incognitoforreview/TileScape/design_files/table design/table underside/webcam mount/0_readme_webcam_mount.pdf

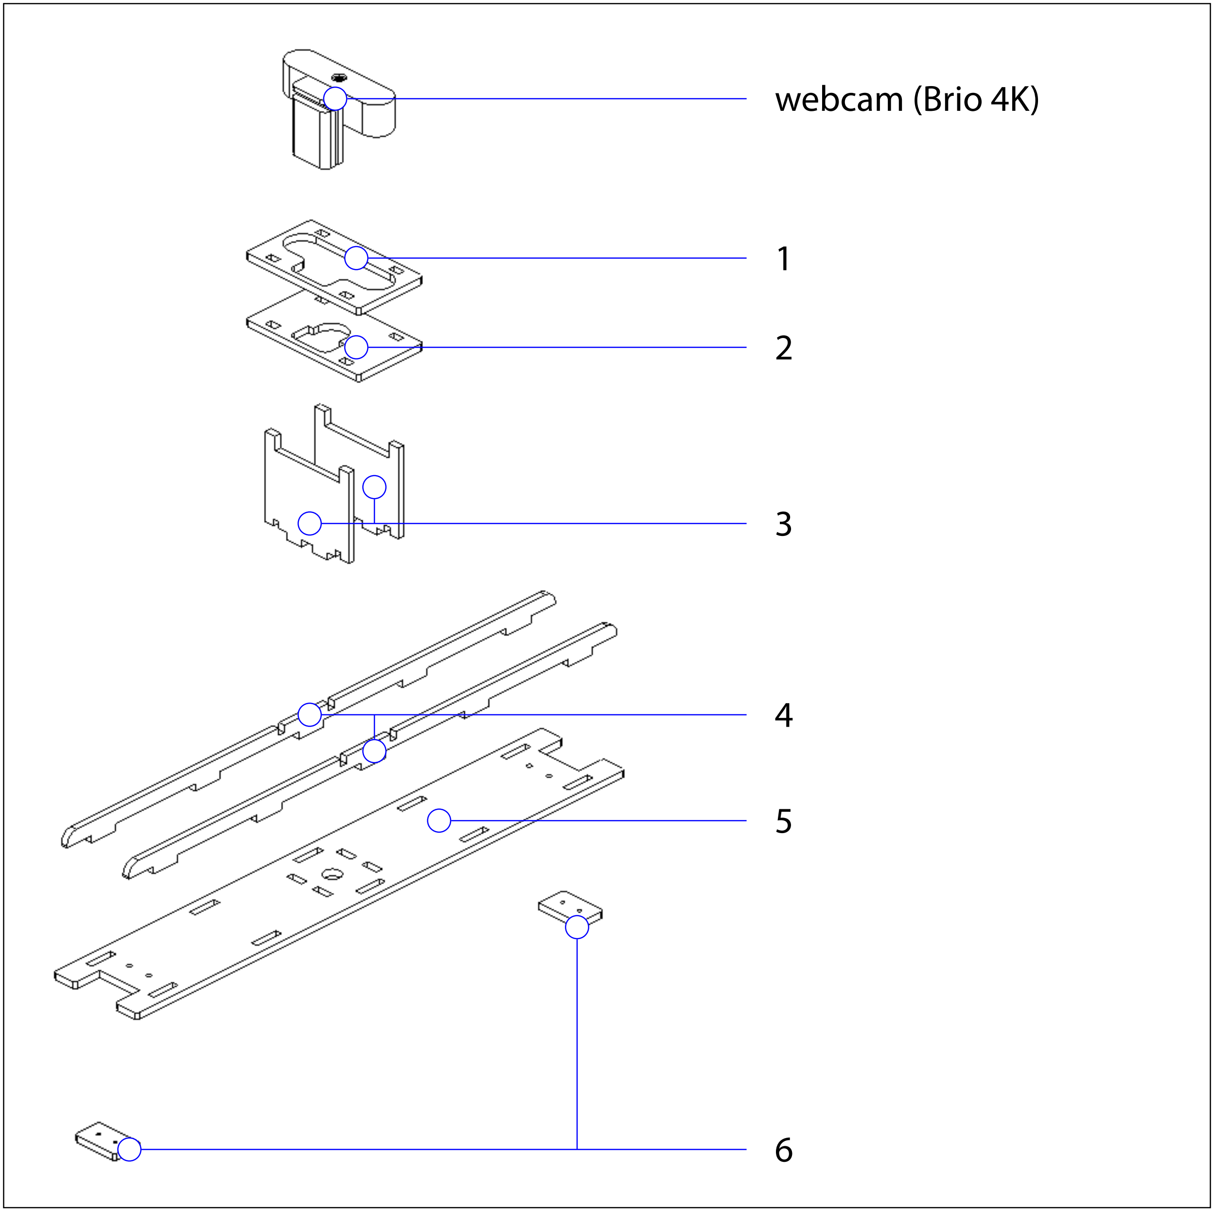
[picture p5: figure]
webcam (Brio 4K)

The les in this folder can be used to create the webcam mount for Tilescape’s tabletop. It is entirely constructed from laser cut shapes out of 6mm
wooden sheets. All shapes are included in a single le for laser cutting these shapes in dierent formats (.dxf, .pdf, .ai). In addition, one .pdf le has annotations in it that align with the numbers shown in the gure to the right.

Once all shapes are cut, the self-align and can be glued together. The exception to this is parts number 6, which are screwed to the middle of the 4_cross_beam_mount_x2 and are used for correct positioning when placing the assembled webcam mount (see gure of full tabletop system). No further nishing of the shapes is required.
