incognitoforreview/TileScape/design_files/table design/table surface/tabletop_frame_3.pdf

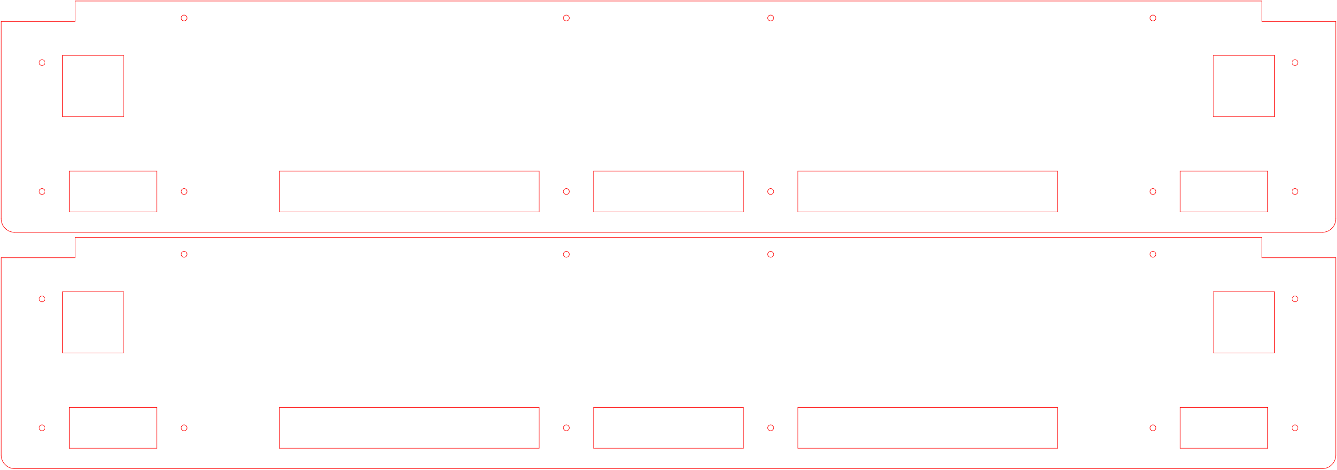
[picture p6: figure]
