incognitoforreview/TileScape/design_files/table design/table surface/tabletop_frame_3_annotated.pdf

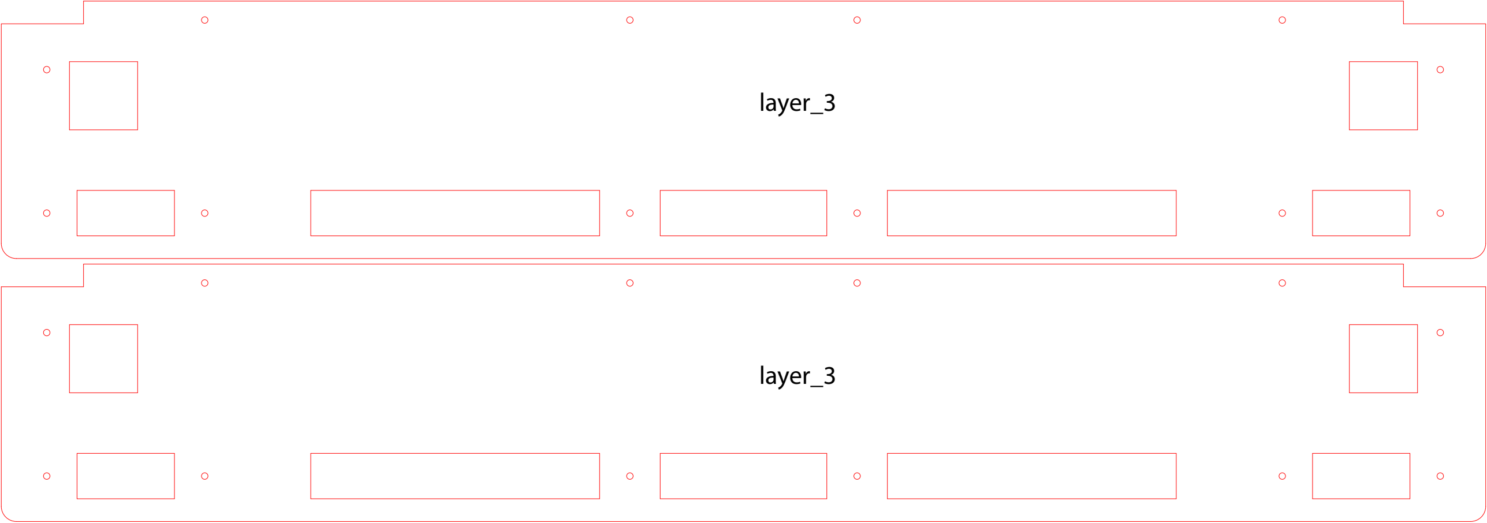
[picture p7: figure]
layer_3
