incognitoforreview/TileScape/design_files/table design/table underside/webcam mount/webcam_mount_laser_cut_shapes.pdf

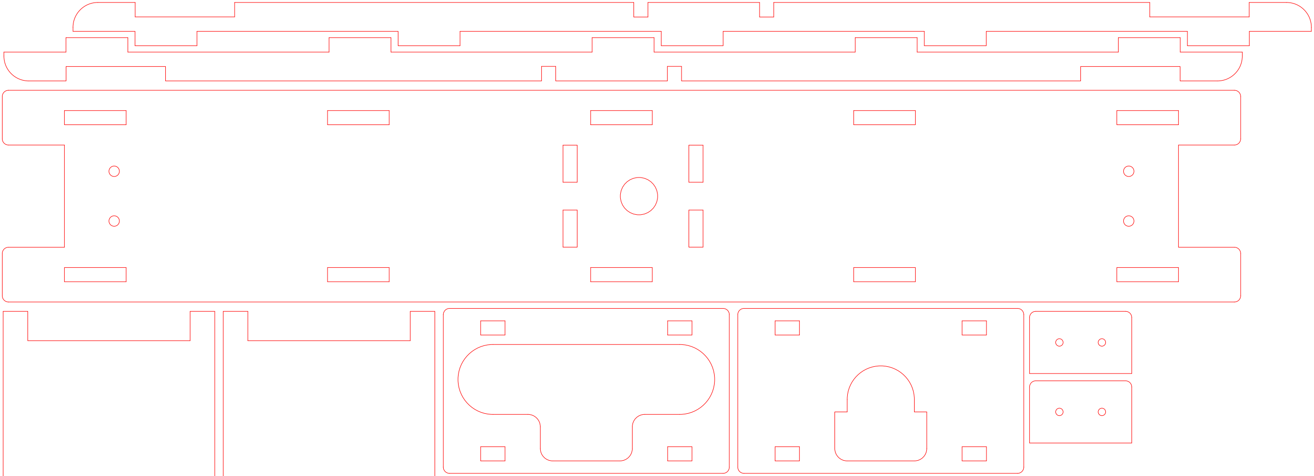
[picture p8: figure]
