incognitoforreview/TileScape/design_files/table design/table underside/webcam mount/webcam_mount_laser_cut_shapes_annotated.pdf

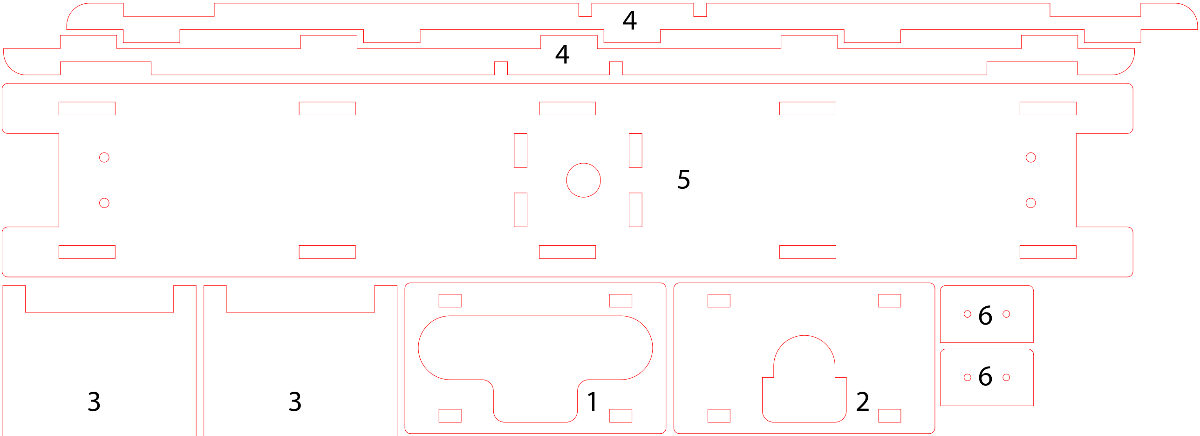
[picture p9: figure]
