incognitoforreview/TileScape/design_files/game pieces designs/3D print templates/2_additional_elevation_template.SLDPRT

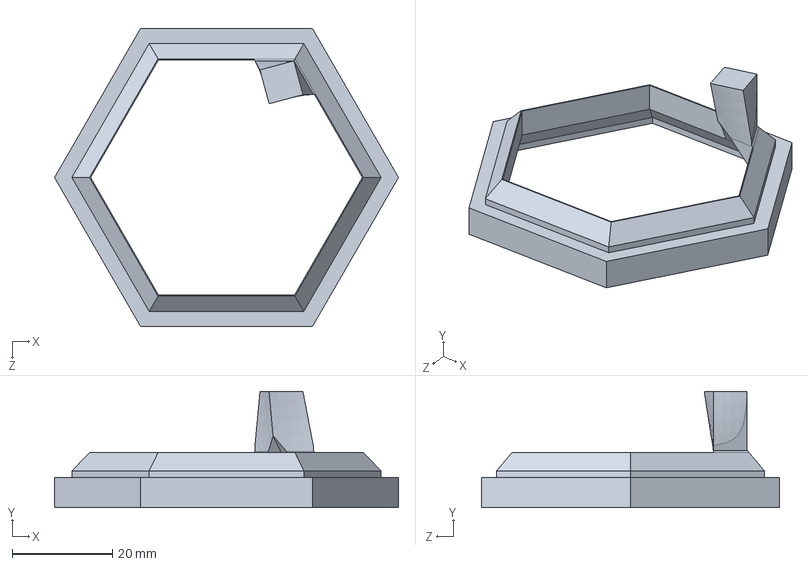
[picture p24: CAD file, 2026-01-09]
design_files/game pieces designs/3D print templates/2_additional_elevation_template.SLDPRT
68.7 x 23.2 x 59.5 mm
