incognitoforreview/TileScape/design_files/game pieces designs/laser cut templates/2_top_piece_base.dxf

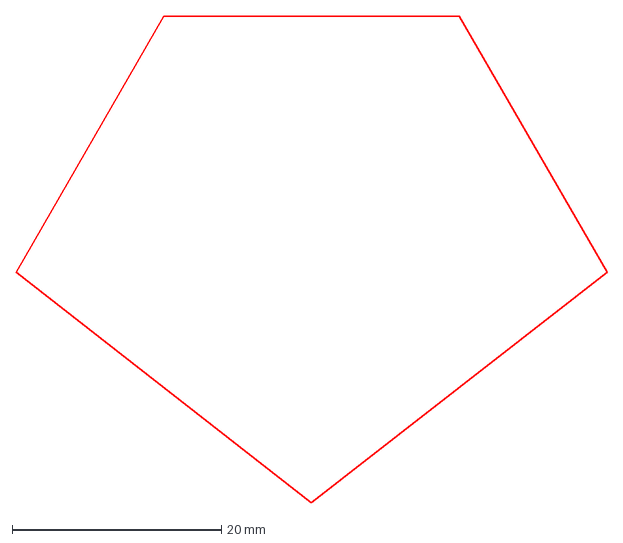
[picture p25: CAD file, 2026-01-09]
design_files/game pieces designs/laser cut templates/2_top_piece_base.dxf
56.5 x 46.5 mm
