incognitoforreview/TileScape/design_files/table design/projector and touchscreen frame/5_cross_beam_top.sldprt

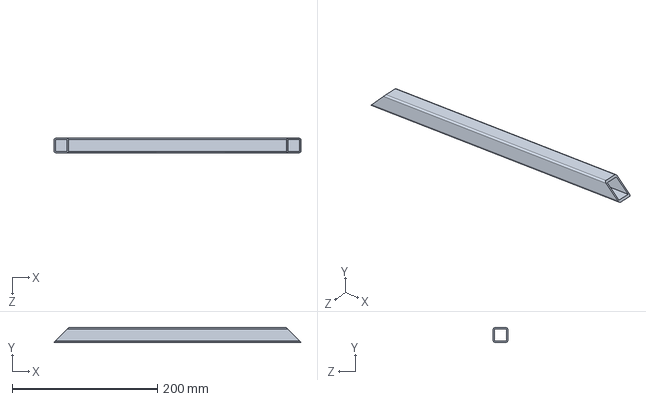
[picture p26: CAD file, 2026-01-09]
design_files/table design/projector and touchscreen frame/5_cross_beam_top.sldprt
340.2 x 20.0 x 20.0 mm
