incognitoforreview/TileScape/design_files/table design/table surface/tabletop_frame_3.dxf

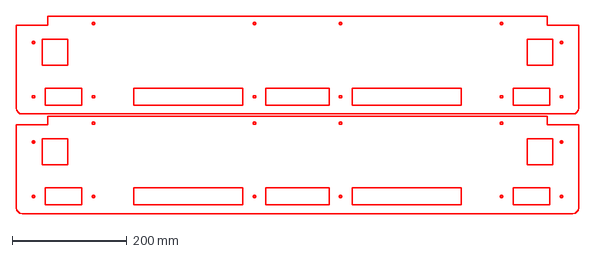
[picture p27: CAD file, 2026-01-09]
design_files/table design/table surface/tabletop_frame_3.dxf
980.0 x 343.6 mm
