incognitoforreview/TileScape/design_files/game pieces designs/laser cut templates/1_height_piece.dxf

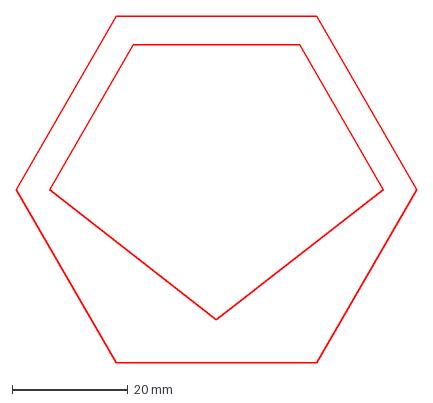
[picture p28: CAD file, 2026-01-09]
design_files/game pieces designs/laser cut templates/1_height_piece.dxf
69.3 x 60.0 mm
