incognitoforreview/TileScape/design_files/table design/table surface/hexagon_grid_6mm.dxf

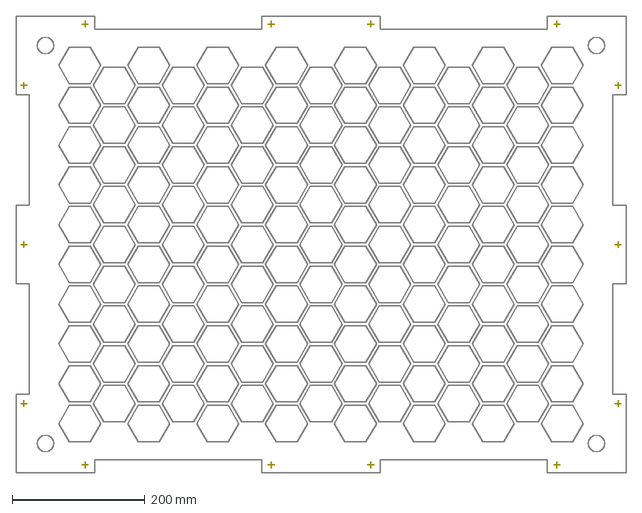
[picture p29: CAD file, 2026-01-09]
design_files/table design/table surface/hexagon_grid_6mm.dxf
920.0 x 689.0 mm
