incognitoforreview/TileScape/design_files/game pieces designs/laser cut templates/3_no_elevation_base.dxf

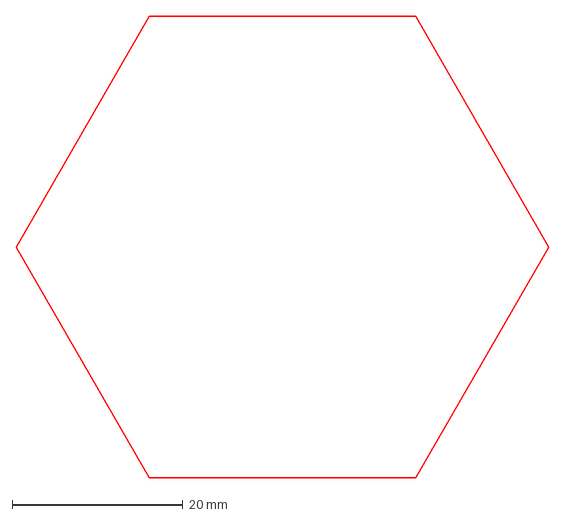
[picture p30: CAD file, 2026-01-09]
design_files/game pieces designs/laser cut templates/3_no_elevation_base.dxf
62.4 x 54.0 mm
