incognitoforreview/TileScape/design_files/table design/table surface/tabletop_frame_5.dxf

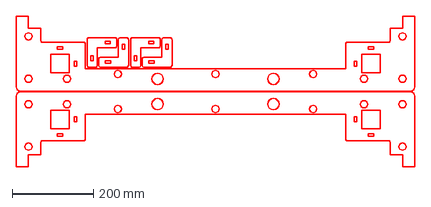
[picture p31: CAD file, 2026-01-09]
design_files/table design/table surface/tabletop_frame_5.dxf
980.0 x 371.0 mm
