incognitoforreview/TileScape/design_files/table design/table underside/legs & frame/0_readme_tabletop_underside_assembly.pdf

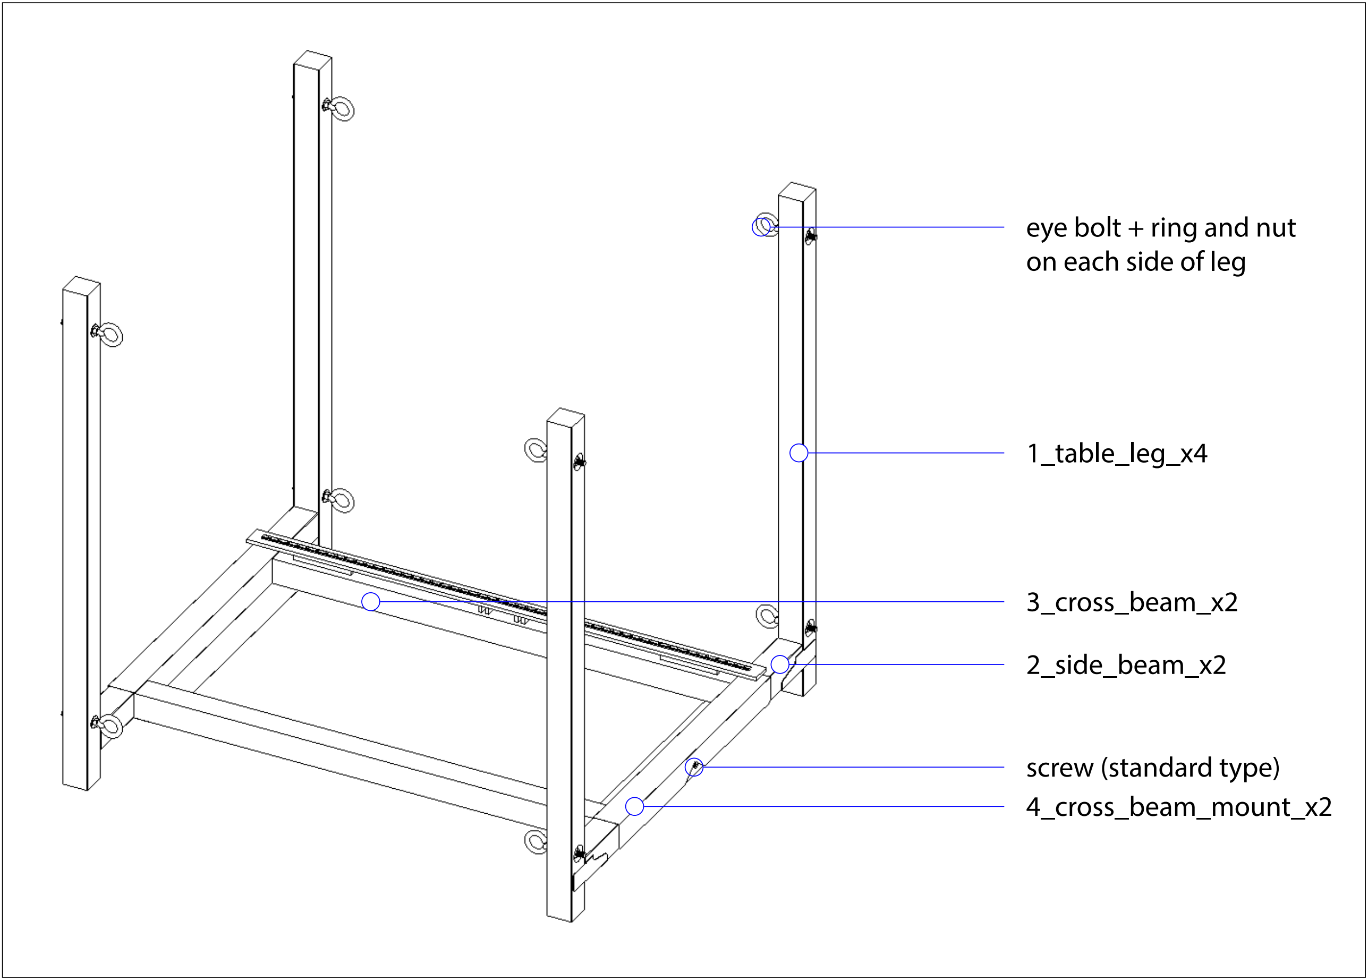
[picture p35: figure]
1_table_leg_x4; eye bolt + ring and nut on each side of leg; 2_side_beam_x2; 4_cross_beam_mount_x2; screw (standard type); 3_cross_beam_x2

The les in this folder can be used to create the legs and frame for mounting Tilescape’s tabletop.
It is mainly constructed from wooden beams and standard connection materials like screws. Only the 4_cross_beam_mount_x2 is manufactured from a 1mm steel plate by means of cutting, bending and drilling.

For construction, the gure on the right shows the assembly underneath the tabletop. In the folder,
the drawings for the beams and dimensions can be found. Two 1_table_leg_x4 and one 2_side_beam_x2 are connected twice to create two U form shapes. We used a metal connection bought at a hardware store (visible in the gure), but simple screws suce. The two 3_cross_beam_x2 are connected with screws to the 4_cross_beam_mount_x2 to create a rectangular shape. Drill holes for this on the bottom side of 4_cross_beam_mount_x2. The two U shapes and rectangular shape can now be placed on each other. We added a simple screw in the middle of
each 2_side_beam_x2 (highlighted in the gure) to help positioning. We recommend painting all wooden beams black with a matte nish before assembly.

The eye bolt, rings and nuts (highlighted in the gure) are used to add 8 connection points for steel cross wires and for the curtain to wrap the table. We used 8mm diameter standard materials from a hardware store.
