incognitoforreview/TileScape/design_files/table design/table surface/tabletop_frame_2.pdf

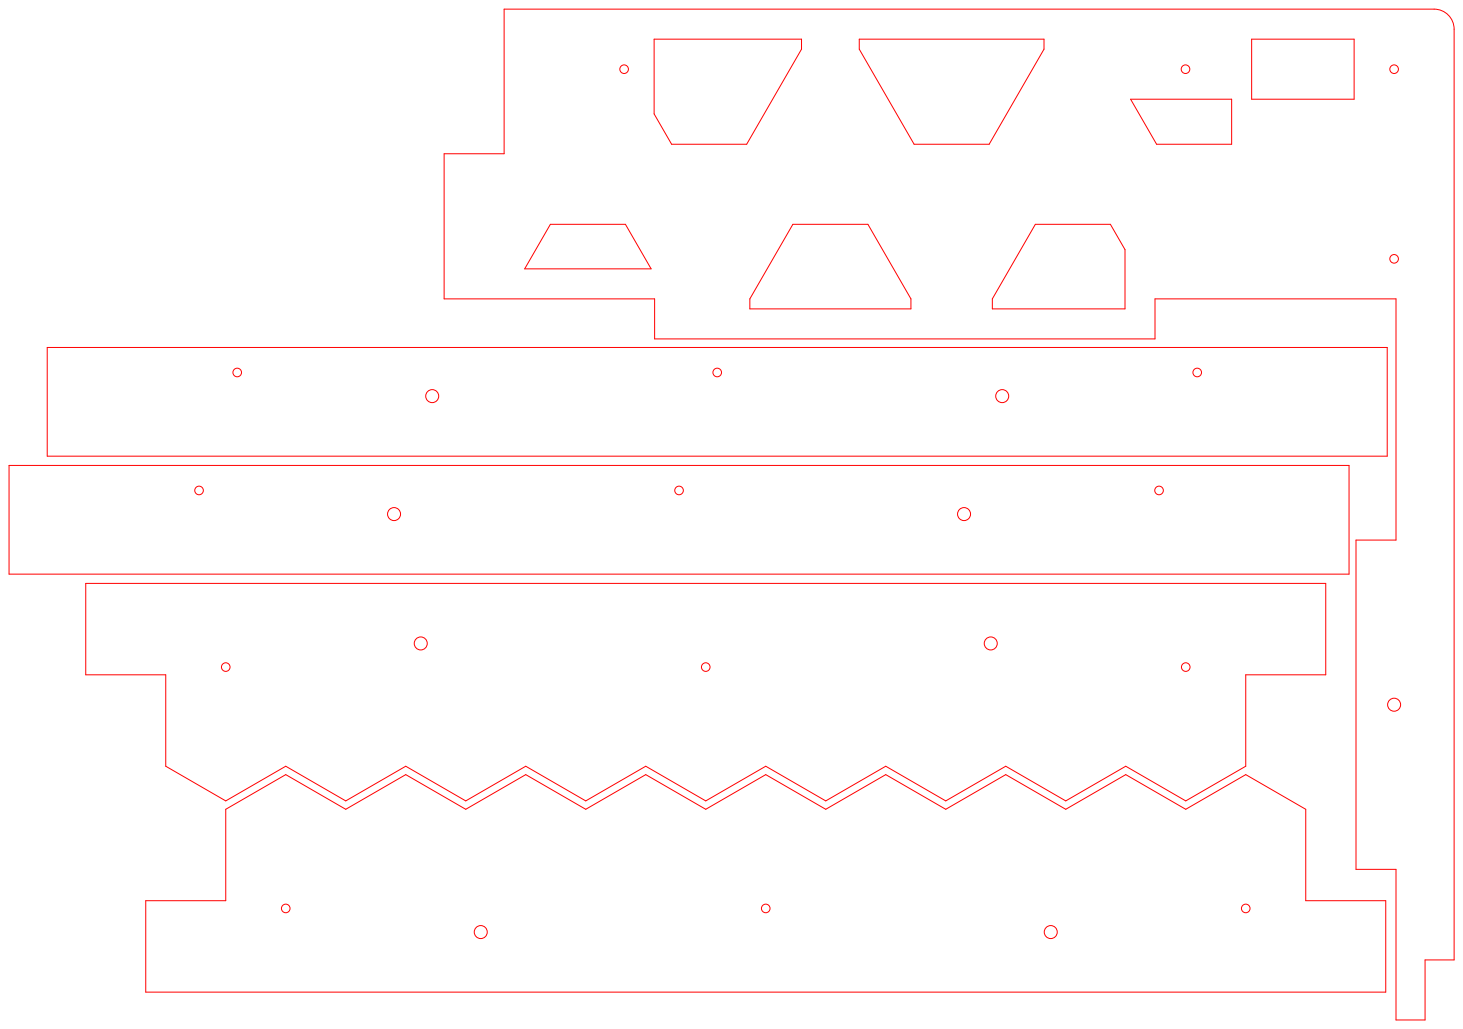
[picture p39: page 1]
