incognitoforreview/TileScape/design_files/table design/table surface/tabletop_frame_2_annotated.pdf

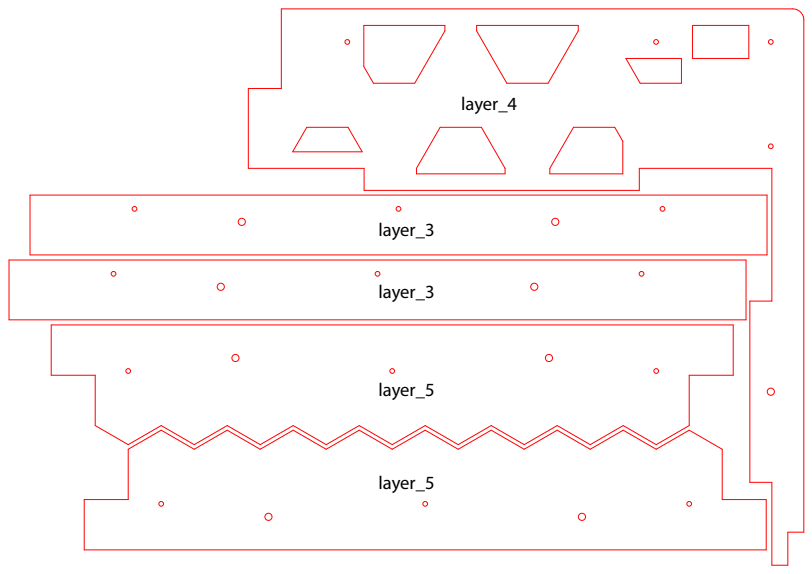
[picture p40: page 1]
layer_4; layer_3; layer_5
