incognitoforreview/TileScape/design_files/table design/table surface/tabletop_frame_4.pdf

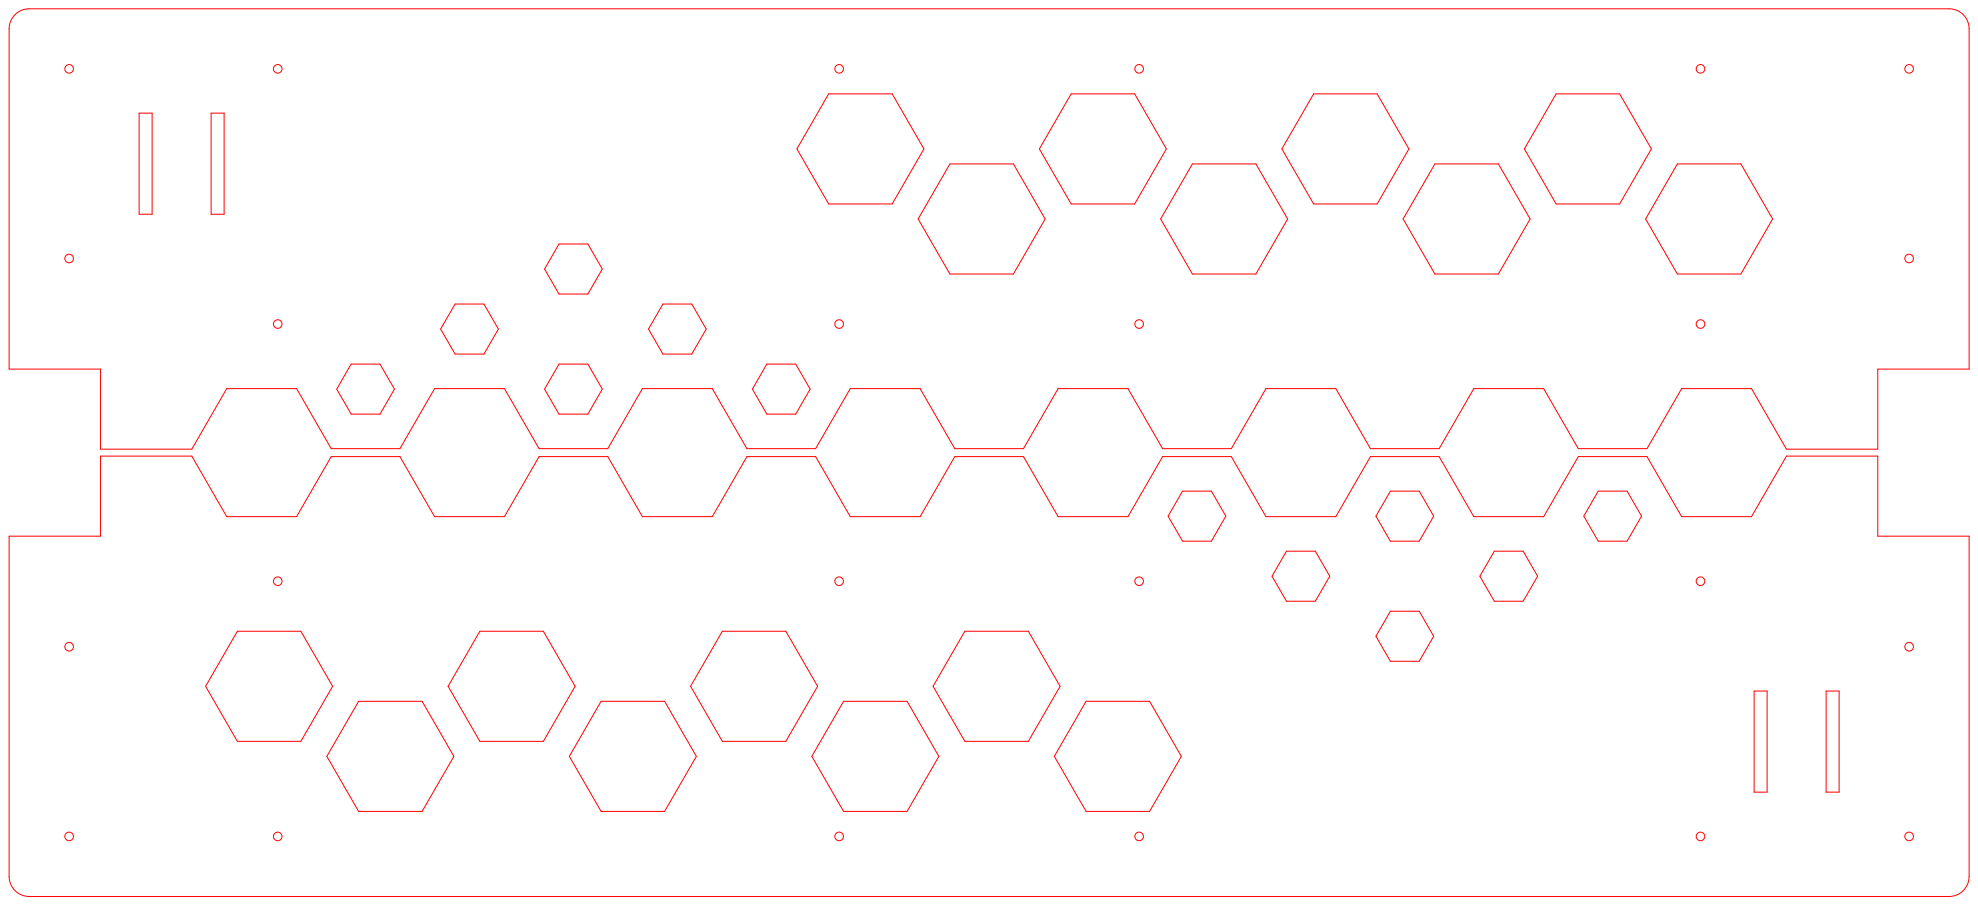
[picture p41: page 1]
