incognitoforreview/TileScape/design_files/table design/table surface/tabletop_frame_4_annotated.pdf

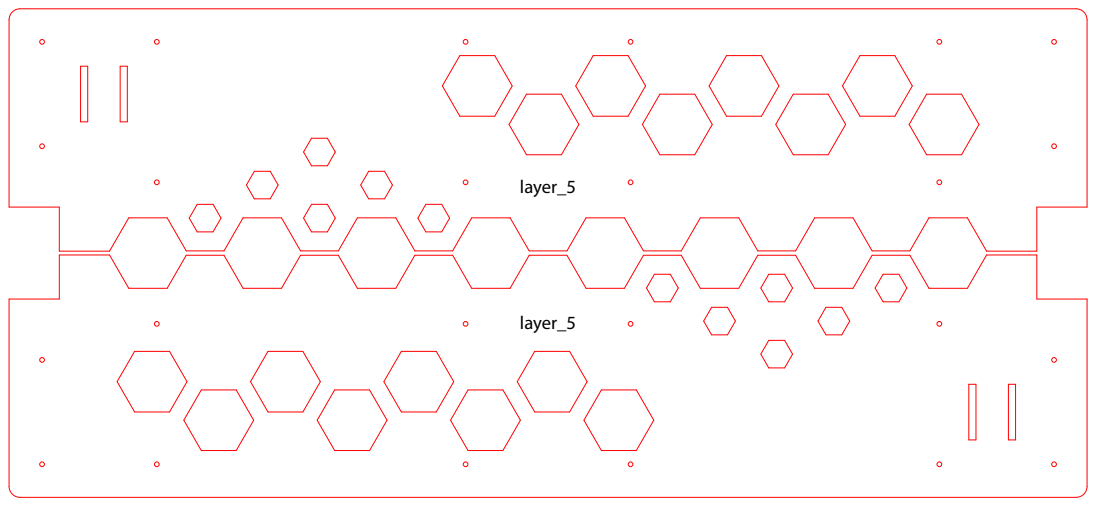
[picture p42: page 1]
layer_5
