incognitoforreview/TileScape/design_files/table design/table surface/tabletop_frame_5.pdf

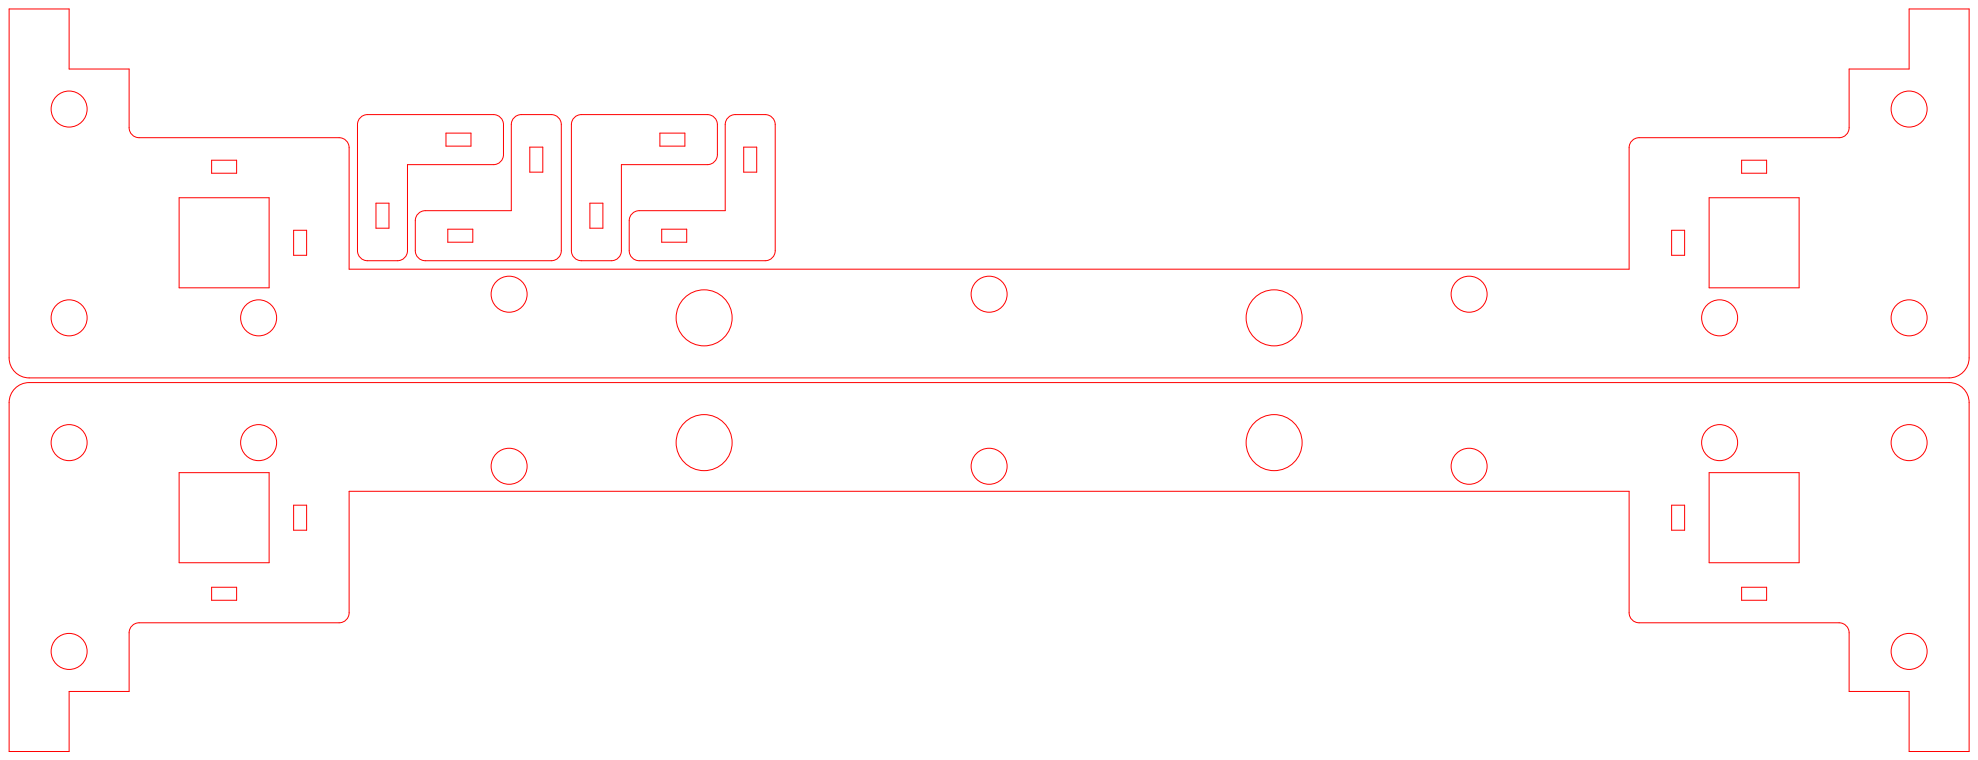
[picture p43: page 1]
