incognitoforreview/TileScape/design_files/table design/table surface/tabletop_frame_5_annotated.pdf

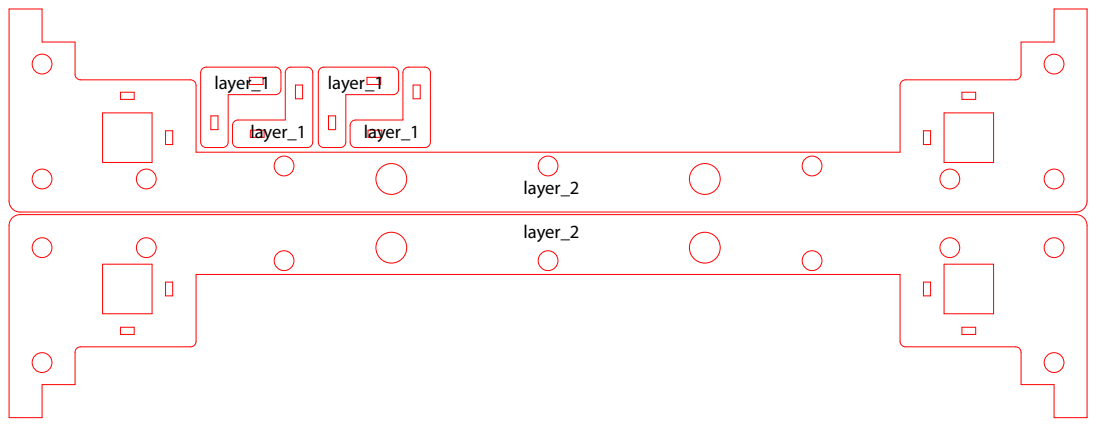
[picture p44: page 1]
layer_2; layer_1
